nk25719/PMD___aka-KiCad-esp32-6leds-2switches-1pj-circuit-/dataSheets/Screenshot 2024-04-13 085957.png

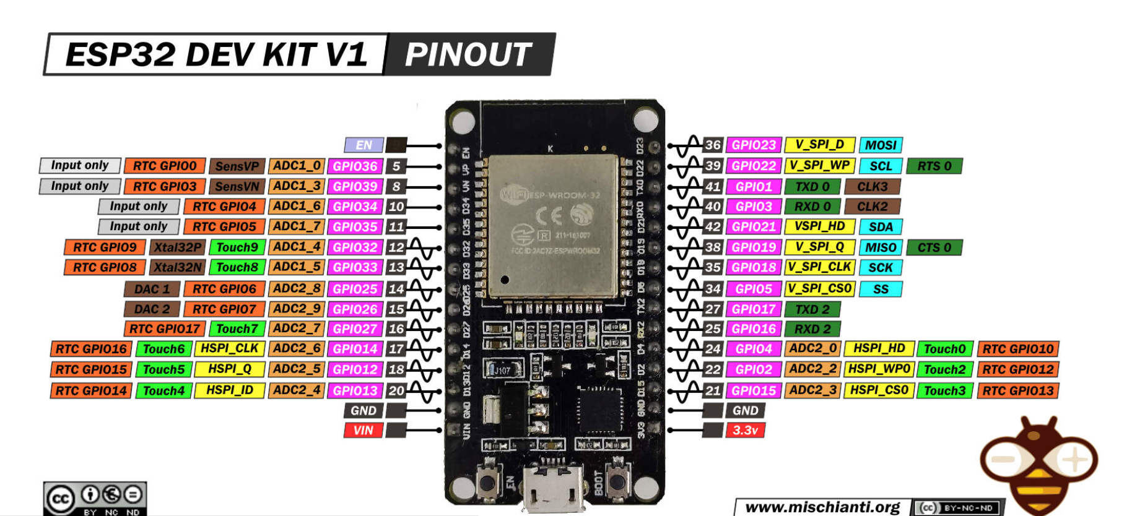
dataSheets/Screenshot 2024-04-13 085957.png
