nk25719/PMD___aka-KiCad-esp32-6leds-2switches-1pj-circuit-/Enclosure_and_Workbench/PMDwWorkbench.jpg

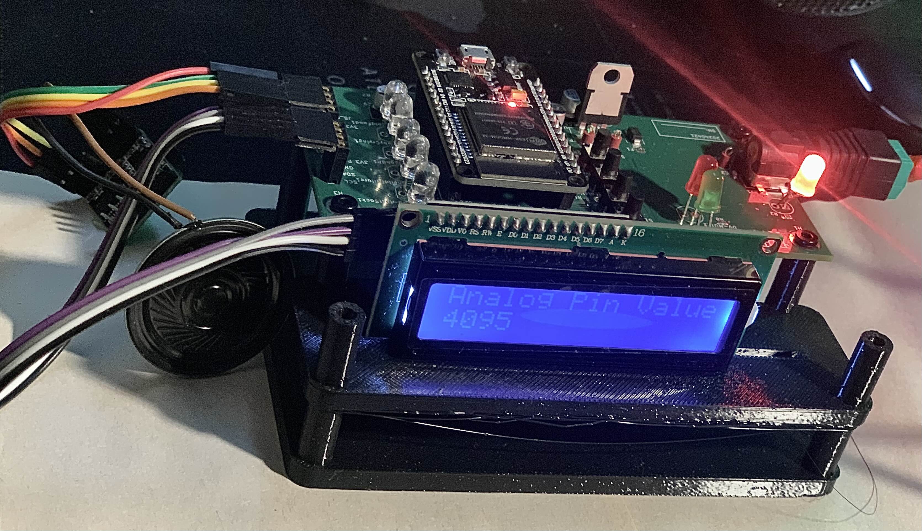
Enclosure_and_Workbench/PMDwWorkbench.jpg
