nk25719/PMD___aka-KiCad-esp32-6leds-2switches-1pj-circuit-/PMD/PMD_WebPage/buttonsAlarmStatus/snakeOil.png

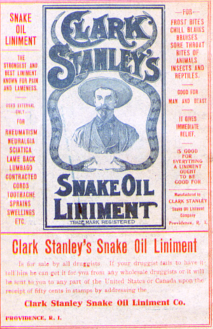
PMD/PMD_WebPage/buttonsAlarmStatus/snakeOil.png
