nk25719/PMD___aka-KiCad-esp32-6leds-2switches-1pj-circuit-/homeWork2/Parts/rj11-connectors-6p-1.snapshot.1/rj-6--horiz-tabdown-615006143621 (rev1).stp

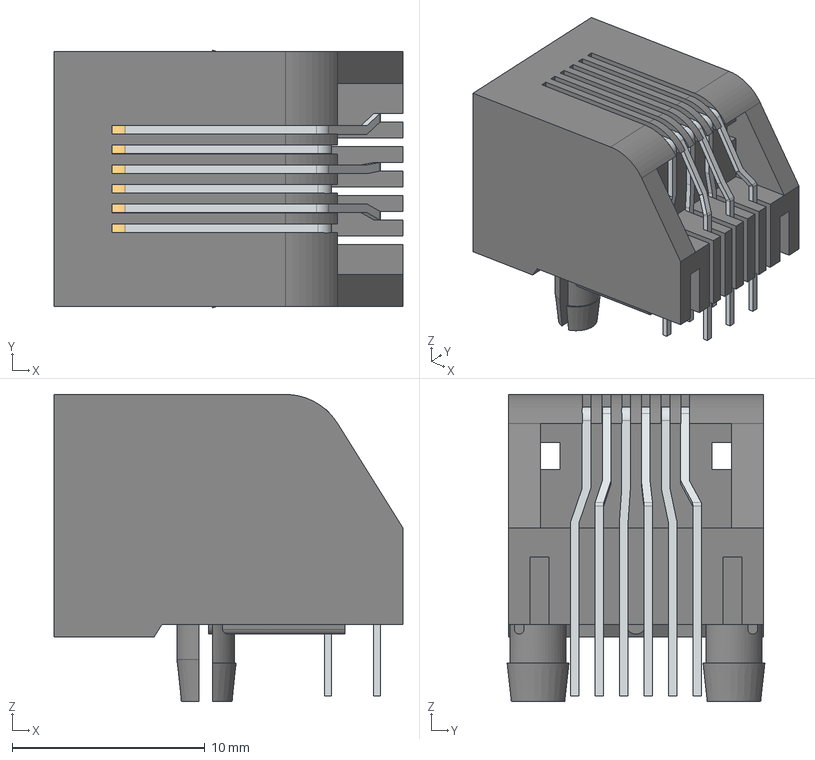
[picture p25: CAD file, 2024-10-27]
homeWork2/Parts/rj11-connectors-6p-1.snapshot.1/rj-6--horiz-tabdown-615006143621 (rev1).stp
18.1 x 13.4 x 15.9 mm
