nk25719/PMD___aka-KiCad-esp32-6leds-2switches-1pj-circuit-/Enclosure_and_Workbench/OLED_Enclosure.3mf

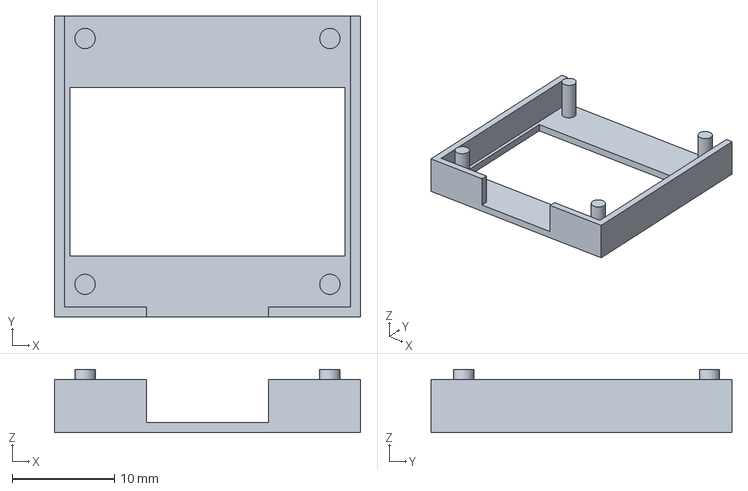
[picture p26: CAD file, 2025-05-12]
Enclosure_and_Workbench/OLED_Enclosure.3mf
30.0 x 29.5 x 6.20 mm
