nk25719/PMD___aka-KiCad-esp32-6leds-2switches-1pj-circuit-/homeWork2/Parts/TS6-THT-SQ.step

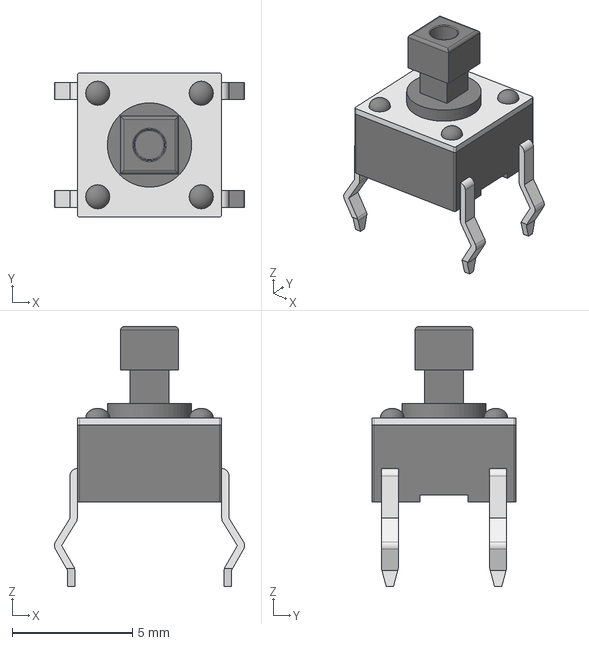
[picture p27: CAD file, 2024-10-27]
homeWork2/Parts/TS6-THT-SQ.step
7.90 x 6.00 x 10.8 mm
