nk25719/PMD___aka-KiCad-esp32-6leds-2switches-1pj-circuit-/Assemblies/NodeMCU-32S.step

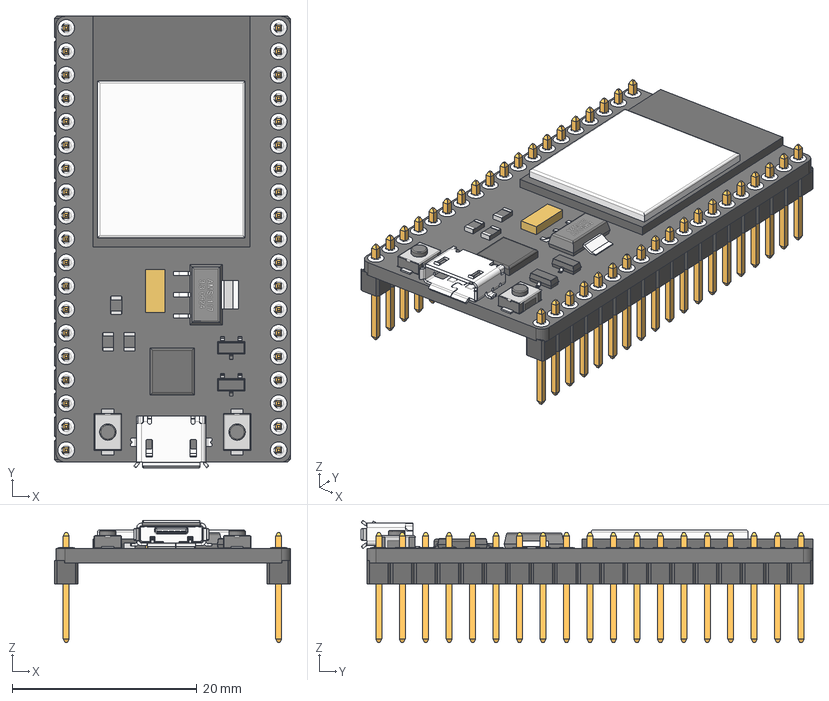
[picture p28: CAD file, 2024-10-19]
Assemblies/NodeMCU-32S.step
25.5 x 48.9 x 13.3 mm
10104111-0001LF v1
zl201-19_p2-54_l48-3_w2-54_h8-9 v1 x 2
res_0805 v1 x 3
res_1206
AMS1117 v1
SOT23SMD v1 x 2
3x4x2mm - 2 Pad v1 x 2
