nk25719/PMD___aka-KiCad-esp32-6leds-2switches-1pj-circuit-/Enclosure_and_Workbench/9mmx5mm_LED_Separator.3mf

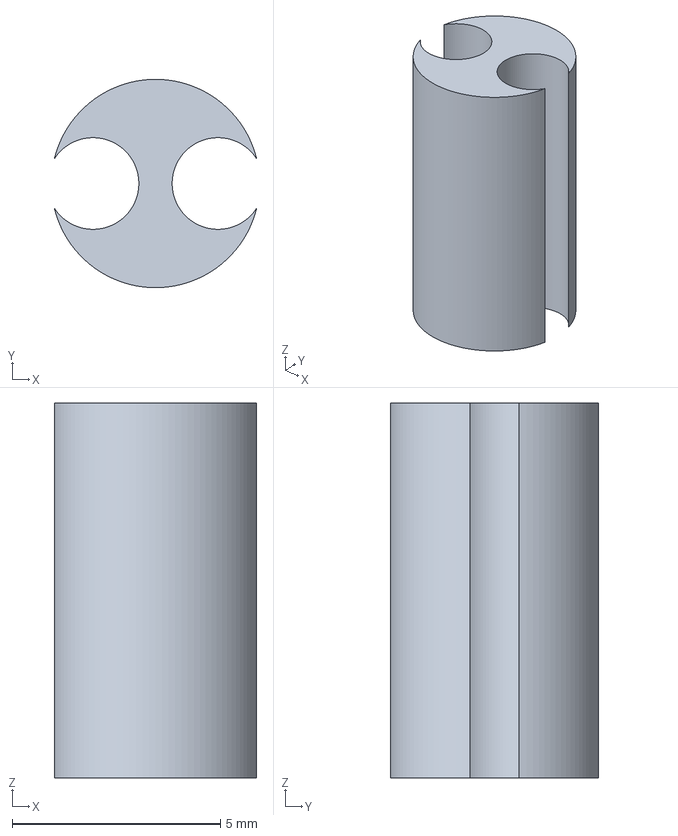
[picture p29: CAD file, 2025-03-29]
Enclosure_and_Workbench/9mmx5mm_LED_Separator.3mf
4.86 x 5.00 x 9.00 mm
