nk25719/PMD___aka-KiCad-esp32-6leds-2switches-1pj-circuit-/homeWork2/Parts/USB User Library-10118194.STEP

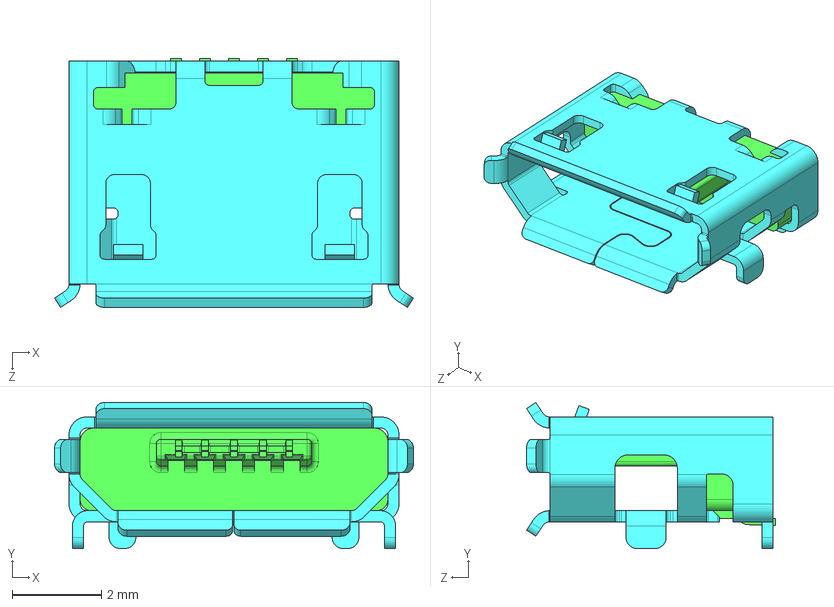
[picture p30: CAD file, 2024-10-27]
homeWork2/Parts/USB User Library-10118194.STEP
8.05 x 3.28 x 5.58 mm
