nk25719/PMD___aka-KiCad-esp32-6leds-2switches-1pj-circuit-/homeWork2/Parts/2004A_ap214.STEP

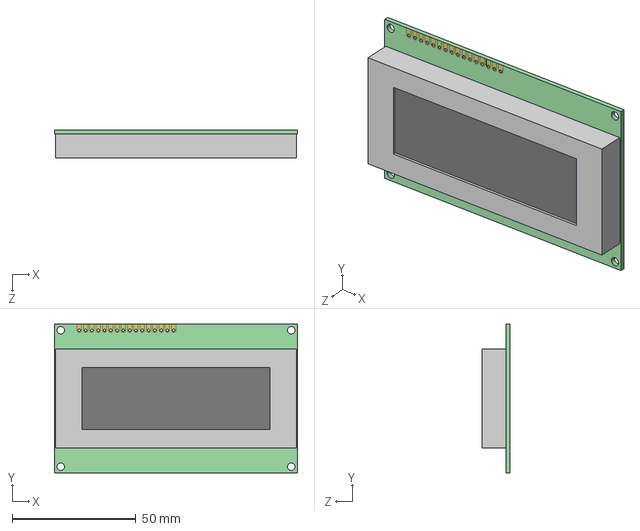
[picture p31: CAD file, 2024-10-27]
homeWork2/Parts/2004A_ap214.STEP
98.0 x 60.0 x 11.1 mm
