nk25719/PMD___aka-KiCad-esp32-6leds-2switches-1pj-circuit-/Enclosure_and_Workbench/EnclosureREVd.3mf

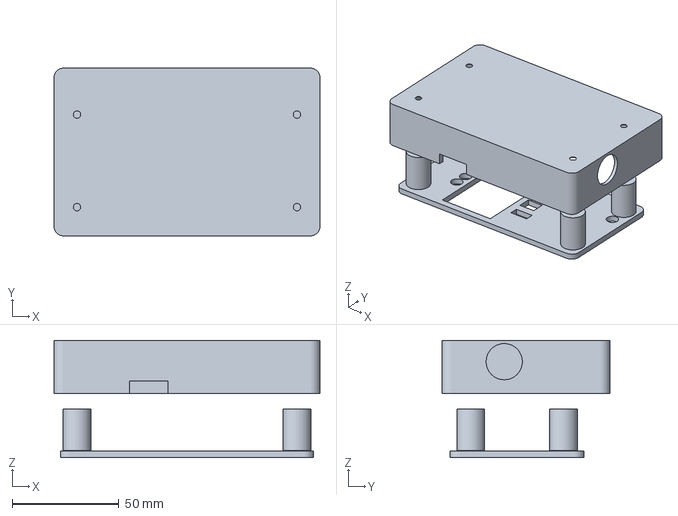
[picture p32: CAD file, 2025-03-29]
Enclosure_and_Workbench/EnclosureREVd.3mf
124.8 x 78.7 x 55.0 mm
