nk25719/PMD___aka-KiCad-esp32-6leds-2switches-1pj-circuit-/homeWork2/Parts/SOT23.STEP

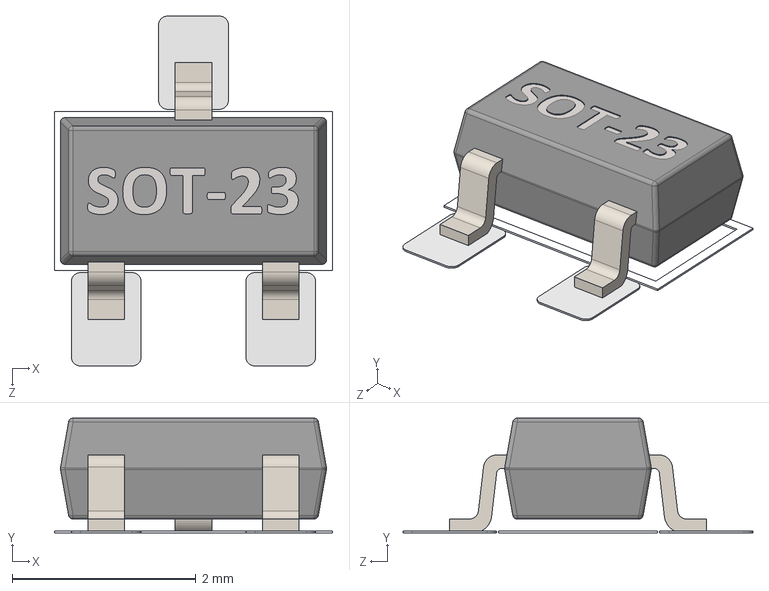
[picture p33: CAD file, 2024-10-27]
homeWork2/Parts/SOT23.STEP
3.03 x 1.25 x 3.81 mm
