nk25719/PMD___aka-KiCad-esp32-6leds-2switches-1pj-circuit-/Enclosure_and_Workbench/LCD_Attachement_1.3mf

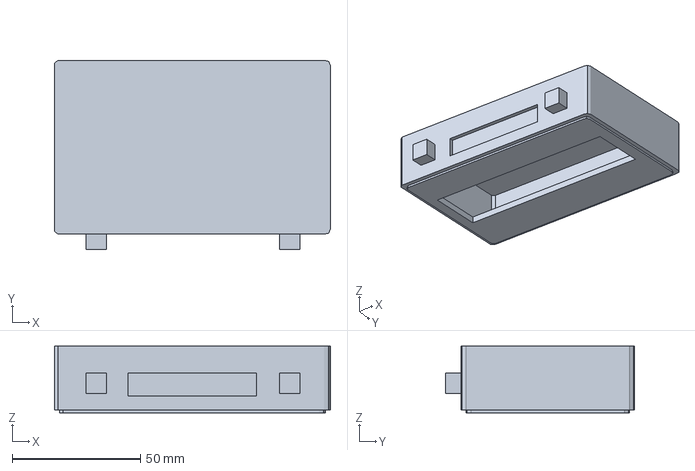
[picture p34: CAD file, 2025-03-29]
Enclosure_and_Workbench/LCD_Attachement_1.3mf
107.8 x 73.9 x 26.0 mm
