nk25719/PMD___aka-KiCad-esp32-6leds-2switches-1pj-circuit-/homeWork2/Parts/BarrelJackSMD v3.step

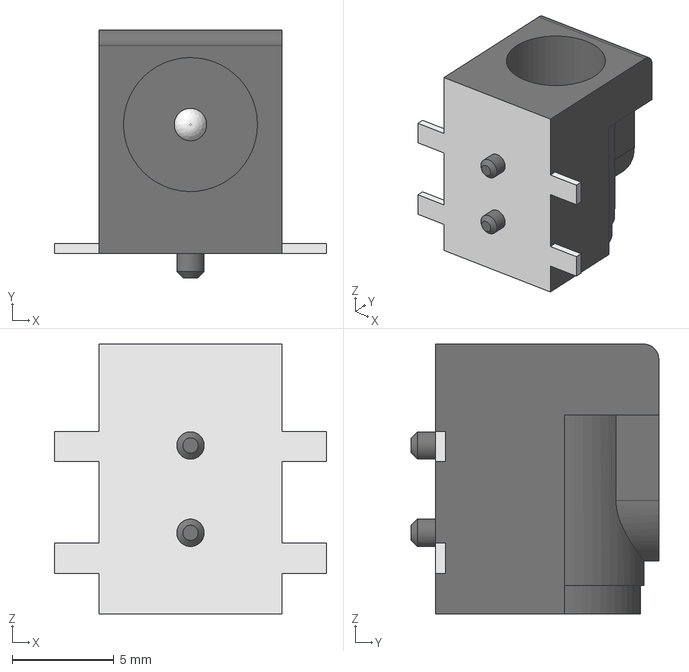
[picture p35: CAD file, 2024-10-27]
homeWork2/Parts/BarrelJackSMD v3.step
13.4 x 12.2 x 13.3 mm
