nk25719/PMD___aka-KiCad-esp32-6leds-2switches-1pj-circuit-/Enclosure_and_Workbench/EnclosureREVc.1.3mf

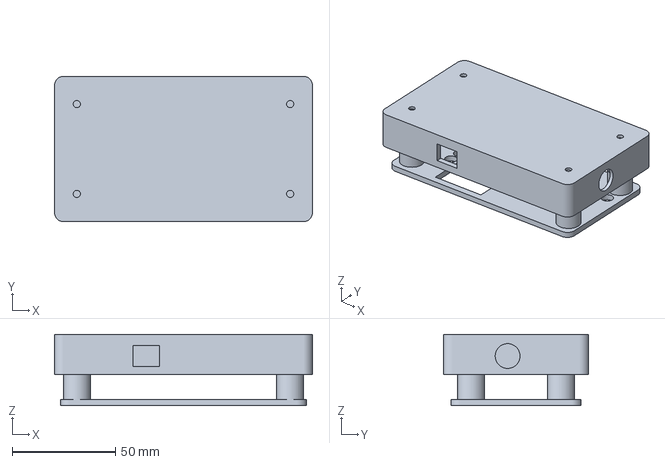
[picture p36: CAD file, 2025-03-29]
Enclosure_and_Workbench/EnclosureREVc.1.3mf
124.8 x 70.4 x 34.5 mm
