nk25719/PMD___aka-KiCad-esp32-6leds-2switches-1pj-circuit-/homeWork2/Parts/NotGood_XKB Connectivity U254-051N-4BH806.step

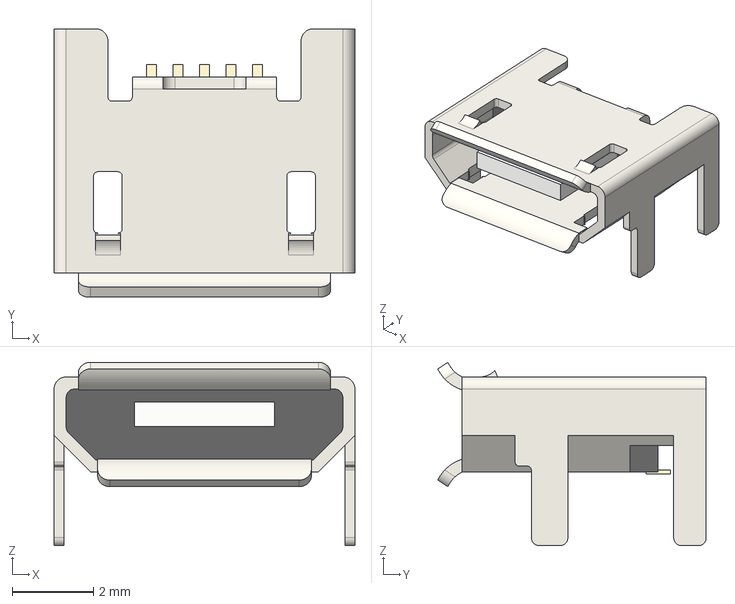
[picture p37: CAD file, 2024-10-27]
homeWork2/Parts/NotGood_XKB Connectivity U254-051N-4BH806.step
7.40 x 6.60 x 4.51 mm
