nk25719/PMD___aka-KiCad-esp32-6leds-2switches-1pj-circuit-/Enclosure_and_Workbench/PMBWorkbench.stl

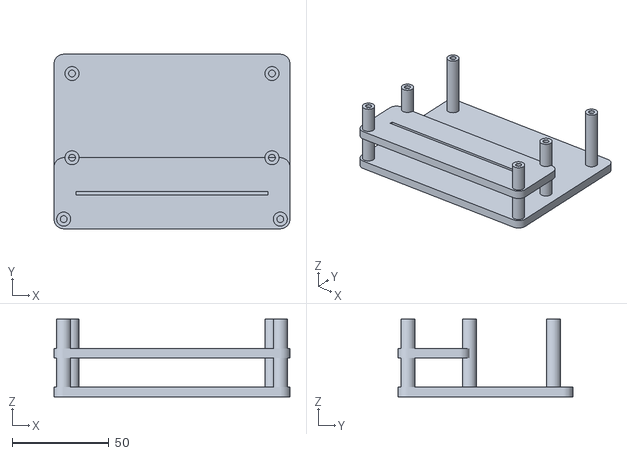
[picture p38: CAD file, 2025-02-20]
Enclosure_and_Workbench/PMBWorkbench.stl
121.8 x 90.0 x 40.0
