nk25719/PMD___aka-KiCad-esp32-6leds-2switches-1pj-circuit-/Enclosure_and_Workbench/5mm_LED_Separator.3mf

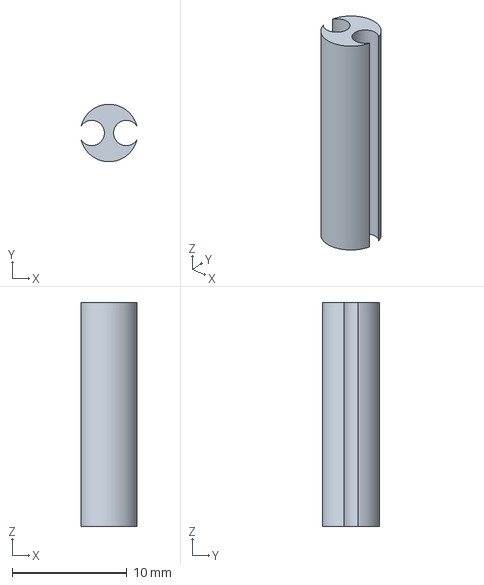
[picture p39: CAD file, 2024-11-25]
Enclosure_and_Workbench/5mm_LED_Separator.3mf
4.86 x 5.00 x 19.5 mm
