nk25719/PMD___aka-KiCad-esp32-6leds-2switches-1pj-circuit-/PMD/PMD_HeartRate/3D Printed Pulse sensor case  - 3383670/images/386260dc76842ec5c13804833cbced2b.png

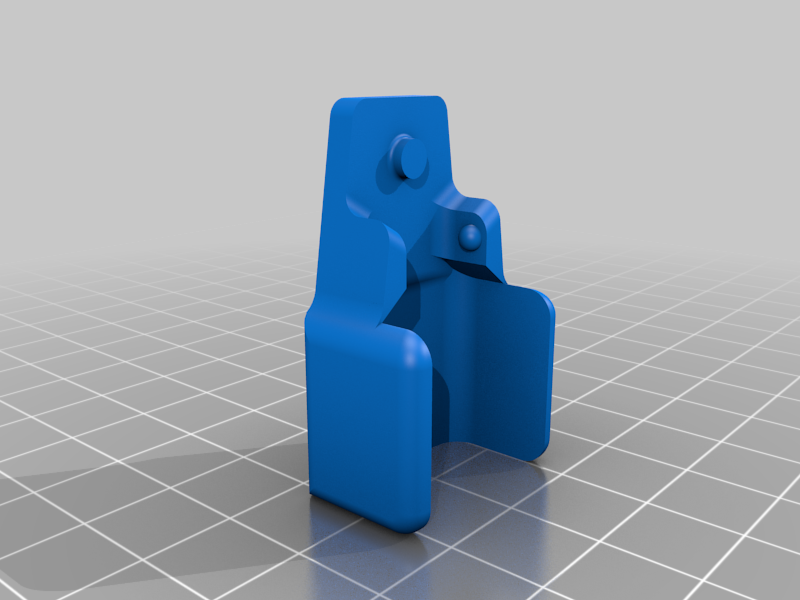
PMD/PMD_HeartRate/3D Printed Pulse sensor case - 3383670/images/386260dc76842ec5c13804833cbced2b.png
