nk25719/PMD___aka-KiCad-esp32-6leds-2switches-1pj-circuit-/PMD/PMD_HeartRate/3D Printed Pulse sensor case  - 3383670/images/20190126161215_IMG_1970.JPG

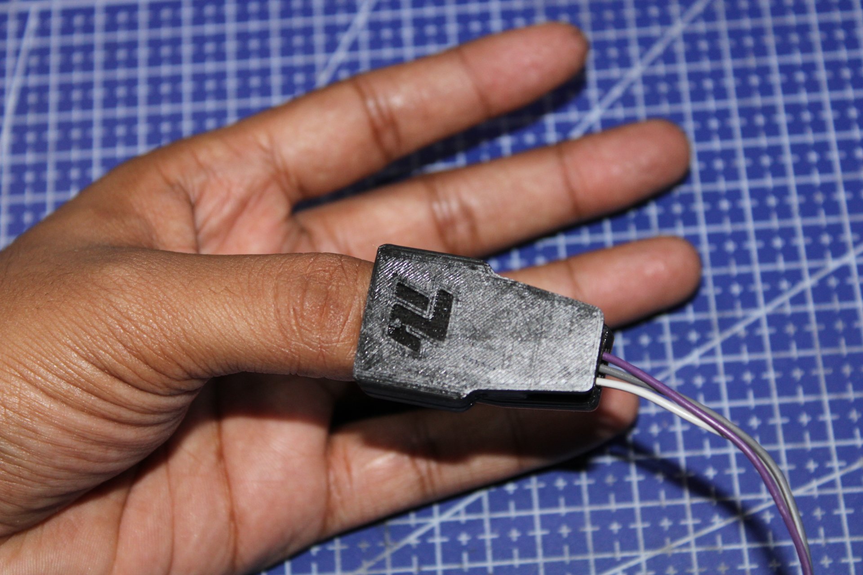
PMD/PMD_HeartRate/3D Printed Pulse sensor case - 3383670/images/20190126161215_IMG_1970.JPG
