nk25719/PMD___aka-KiCad-esp32-6leds-2switches-1pj-circuit-/PMD/PMD_HeartRate/3D Printed Pulse sensor case  - 3383670/images/20190126161249_IMG_1974.JPG

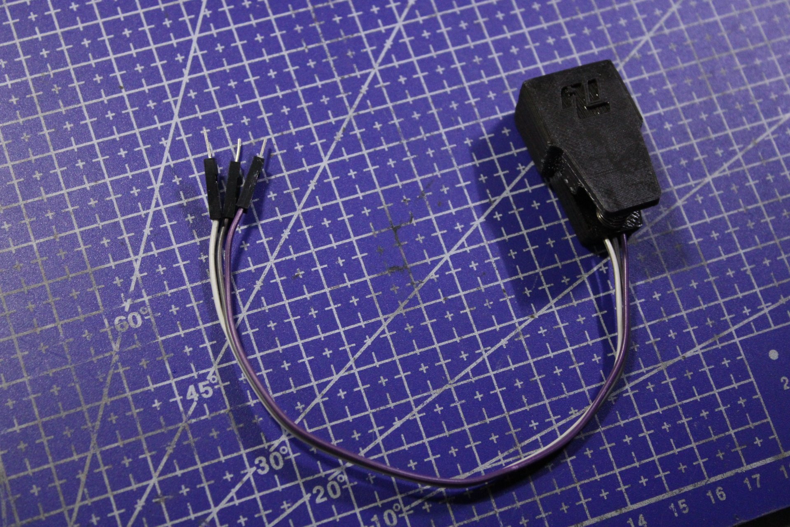
PMD/PMD_HeartRate/3D Printed Pulse sensor case - 3383670/images/20190126161249_IMG_1974.JPG
