nk25719/PMD___aka-KiCad-esp32-6leds-2switches-1pj-circuit-/PMD/PMD_BOOTUP/Wink.ino

// 
// Author: Forrest Lee Erickson
// Date: 20241013
// LICENSE "GNU Affero General Public License, version 3 "



// Heart beat aka activity indicator LED.
//Set LED for Uno or ESP32 Dev Kit on board blue LED.
//const int LED_BUILTIN = 2;    // ESP32 Kit

//const int LED_BUILTIN = 13;    //Not really needed for Arduino UNO it is defined in library
const int HIGH_TIME_LED = 900;
const int LOW_TIME_LED = 100;
unsigned long lastLEDtime = 0;
unsigned long nextLEDchange = 100; //time in ms.

//Wink the LED
void wink(void) {
  if (((millis() - lastLEDtime) > nextLEDchange) || (millis() < lastLEDtime)) {
    if (digitalRead(LED_BUILTIN) == LOW) {
      digitalWrite(LED_BUILTIN, HIGH);   // turn the LED on (HIGH is the voltage level)
      nextLEDchange = HIGH_TIME_LED;
    } else {
      digitalWrite(LED_BUILTIN, LOW);   // turn the LED on (HIGH is the voltage level)
      nextLEDchange = LOW_TIME_LED;
    }
    lastLEDtime = millis();
  }
}//end LED wink
