nk25719/PMD___aka-KiCad-esp32-6leds-2switches-1pj-circuit-/PMD/PMD_BPM/BPM.h

#ifndef PULSECOUNTER_H
#define PULSECOUNTER_H

#include <Arduino.h>

class PulseCounter {
public:
  PulseCounter(int sensorPin, int ledPin, int threshold, unsigned long intervalMs);
  void begin();
  int update();

private:
  int _sensorPin;
  int _ledPin;
  int _threshold;
  unsigned long _interval;
  unsigned long _startTime;
  int _count;
  int _BPM ;
};

#endif
