nk25719/PMD___aka-KiCad-esp32-6leds-2switches-1pj-circuit-/PMD/PMD_BPM/ID.h

#include <Arduino.h>


#define VERSION " V.0.1.2 "
//#define MODEL_NAME "Model: BUTTOM"
#define MODEL_NAME "Model: HW2_WiFiReady_Elegant"
#define DEVICE_UNDER_TEST "SN: 00001"
#define LICENSE "GNU Affero General Public License, version 3 "
#define ORIGIN "LB"
