nk25719/PMD___aka-KiCad-esp32-6leds-2switches-1pj-circuit-/FactoryTest/learnMultitaskingMillis/Blink6inSequence_jul20a/Blink6inSequence_jul20a.ino

      /*
  Blink
  Turns on an LED on for one second, then off for one second, repeatedly.
 
  This example code is in the public domain.
 */
 
// Pin 13 has an LED connected on most Arduino boards.
// give it a name:
// int led = 13; //UNO LED 

int led = 4;
int led1 = 15;
int led2 = 2;
int led3 = 5;
int led4 = 18;
int led5 = 19;


// the setup routine runs once when you press reset:
void setup() {                
  // initialize the digital pin as an output.
  pinMode(led, OUTPUT);     
  pinMode(led1, OUTPUT); 
  pinMode(led2, OUTPUT); 
  pinMode(led3, OUTPUT); 
  pinMode(led4, OUTPUT); 
  pinMode(led5, OUTPUT); 
}

// the loop routine runs over and over again forever:
void loop() {
  digitalWrite(led, HIGH);   // turn the LED on (HIGH is the voltage level)
  delay(1000);               // wait for a second
  digitalWrite(led, LOW);    // turn the LED off by making the voltage LOW
  delay(1000);               // wait for a second
  
   digitalWrite(led1, HIGH);   // turn the LED on (HIGH is the voltage level)
  delay(500);               // wait for a second
  digitalWrite(led1, LOW);    // turn the LED off by making the voltage LOW
  delay(500);               // wait for a second

     digitalWrite(led2, HIGH);   // turn the LED on (HIGH is the voltage level)
  delay(500);               // wait for a second
  digitalWrite(led2, LOW);    // turn the LED off by making the voltage LOW
  delay(500);   

   digitalWrite(led3, HIGH);   // turn the LED on (HIGH is the voltage level)
  delay(500);               // wait for a second
  digitalWrite(led3, LOW);    // turn the LED off by making the voltage LOW
  delay(500);   

     digitalWrite(led4, HIGH);   // turn the LED on (HIGH is the voltage level)
  delay(500);               // wait for a second
  digitalWrite(led4, LOW);    // turn the LED off by making the voltage LOW
  delay(500);   

     digitalWrite(led5, HIGH);   // turn the LED on (HIGH is the voltage level)
  delay(500);               // wait for a second
  digitalWrite(led5, LOW);    // turn the LED off by making the voltage LOW
  delay(500);   











}
    
